fablab-wue/piTelex.supplement/PCB_KiCad/piTelex_TW39_2.1.0/PDF/piTelex_TW39_2.1.0.pdf

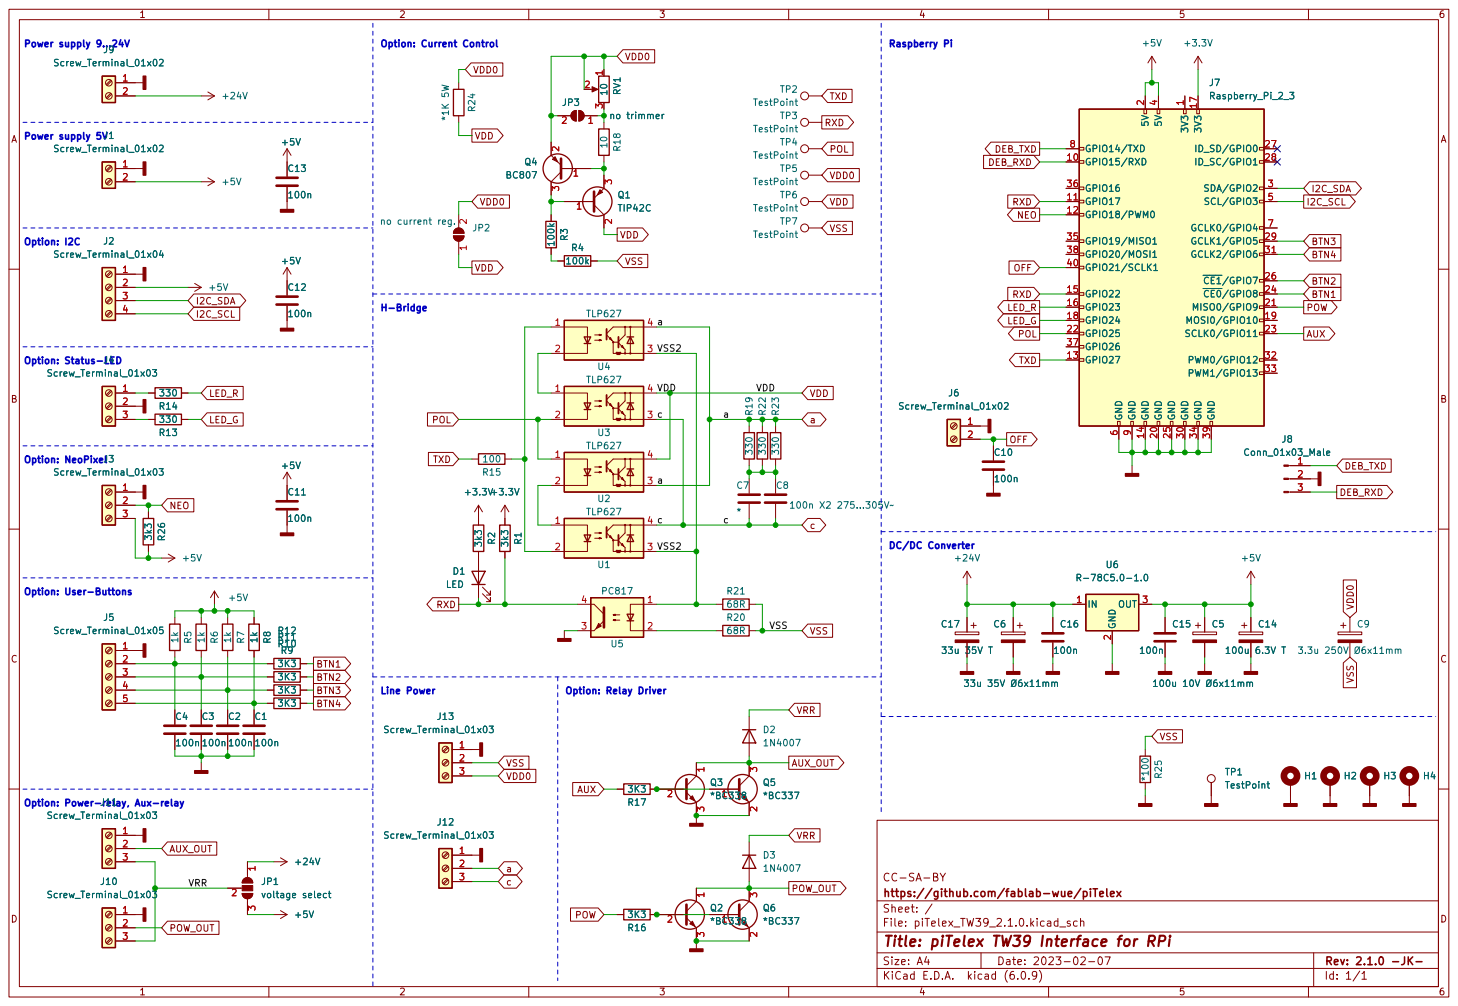
[picture p4: page 1]

File: piTelex_TW39_2.1.0.kicad_sch Sheet: / https://github.com/fablab-wue/piTelex CC-SA-BY

Id: 1/1 Title: piTelex TW39 Interface for RPi
