fablab-wue/piTelex.supplement/PCB_KiCad/SEU-M_1.04/PDF/SEU-M_1.04-B_Cu.pdf

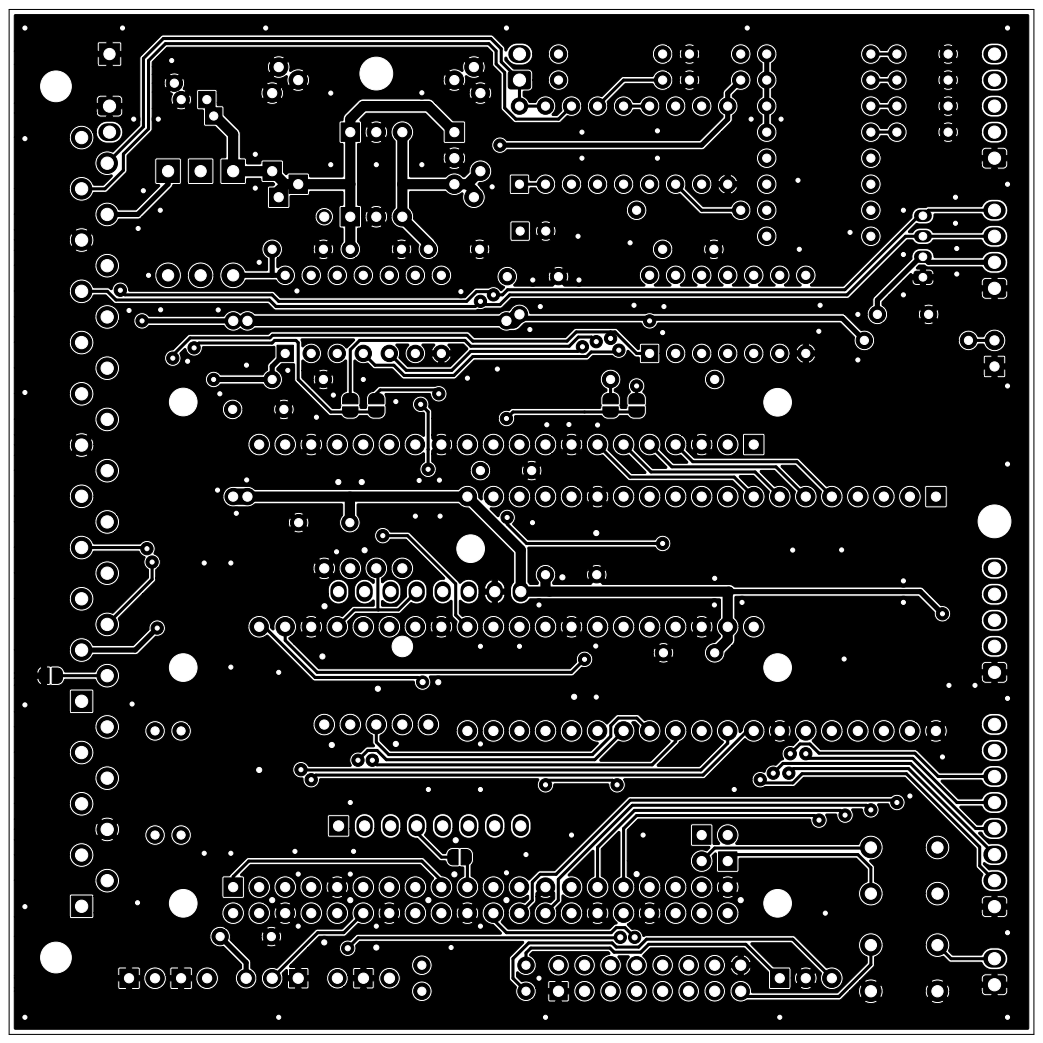
[picture p5: page 1]

File: SEU-M_1.04.kicad_pcb Sheet: Open Hardware
