fablab-wue/piTelex.supplement/PCB_KiCad/SEU-M_1.04/PDF/SEU-M_1.04-F_Cu.pdf

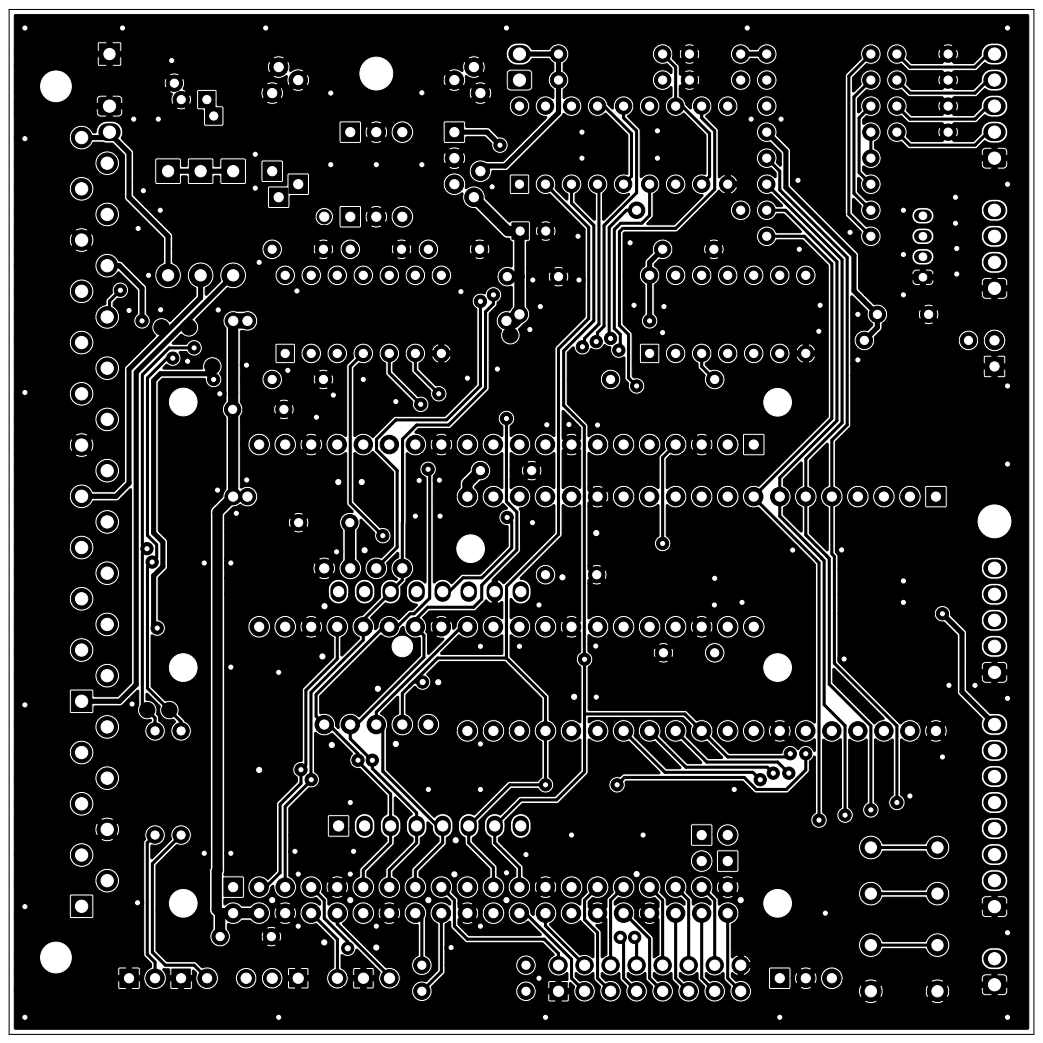
[picture p6: page 1]

File: SEU-M_1.04.kicad_pcb Sheet: Open Hardware
