fablab-wue/piTelex.supplement/PCB_KiCad/SEU-M_1.04/PDF/SEU-M_1.04-F_Fab.pdf

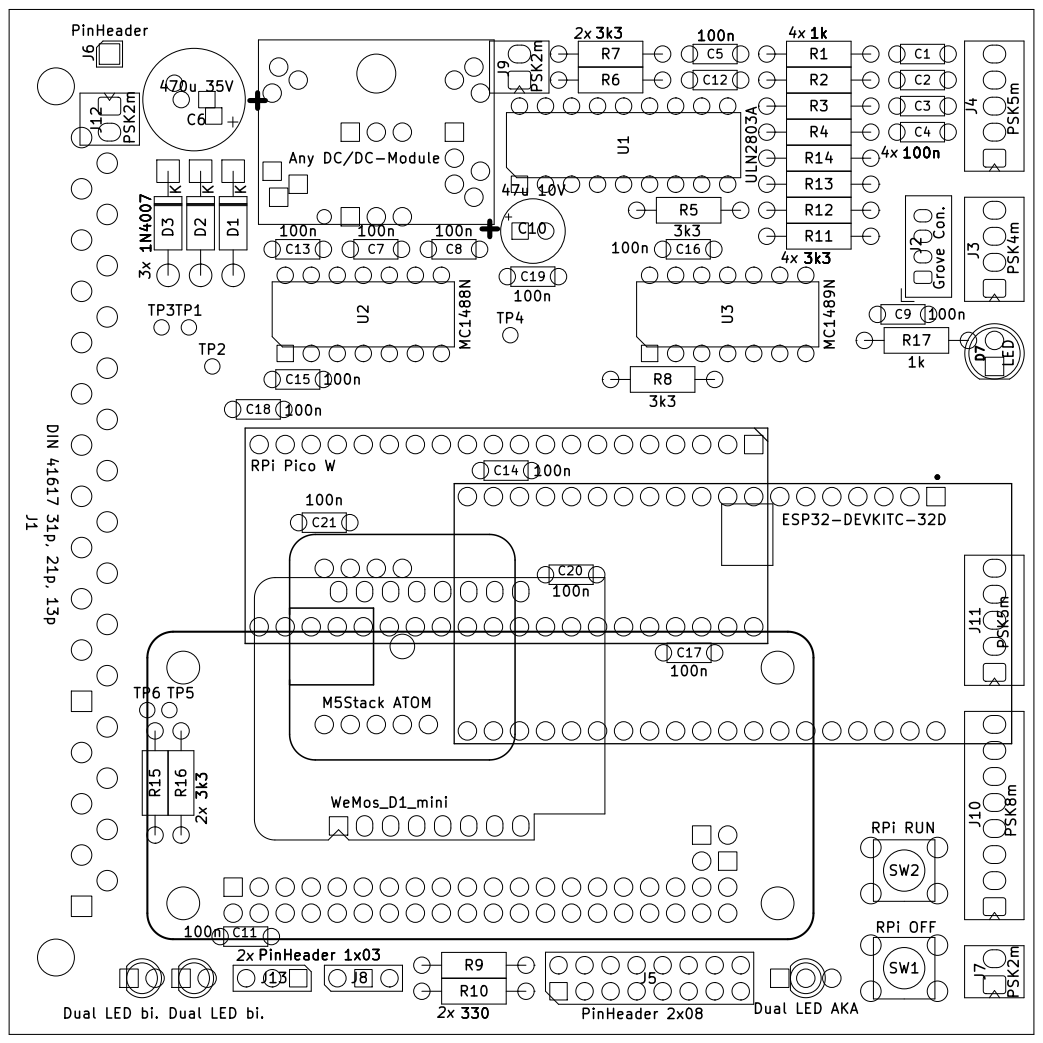
[picture p7: page 1]

SW2 Dual LED bi. PinHeader 1x03

File: SEU-M_1.04.kicad_pcb Sheet: Open Hardware
