fablab-wue/piTelex.supplement/PCB_KiCad/SEU-M_1.04/PDF/SEU-M_1.04-F_Silkscreen.pdf

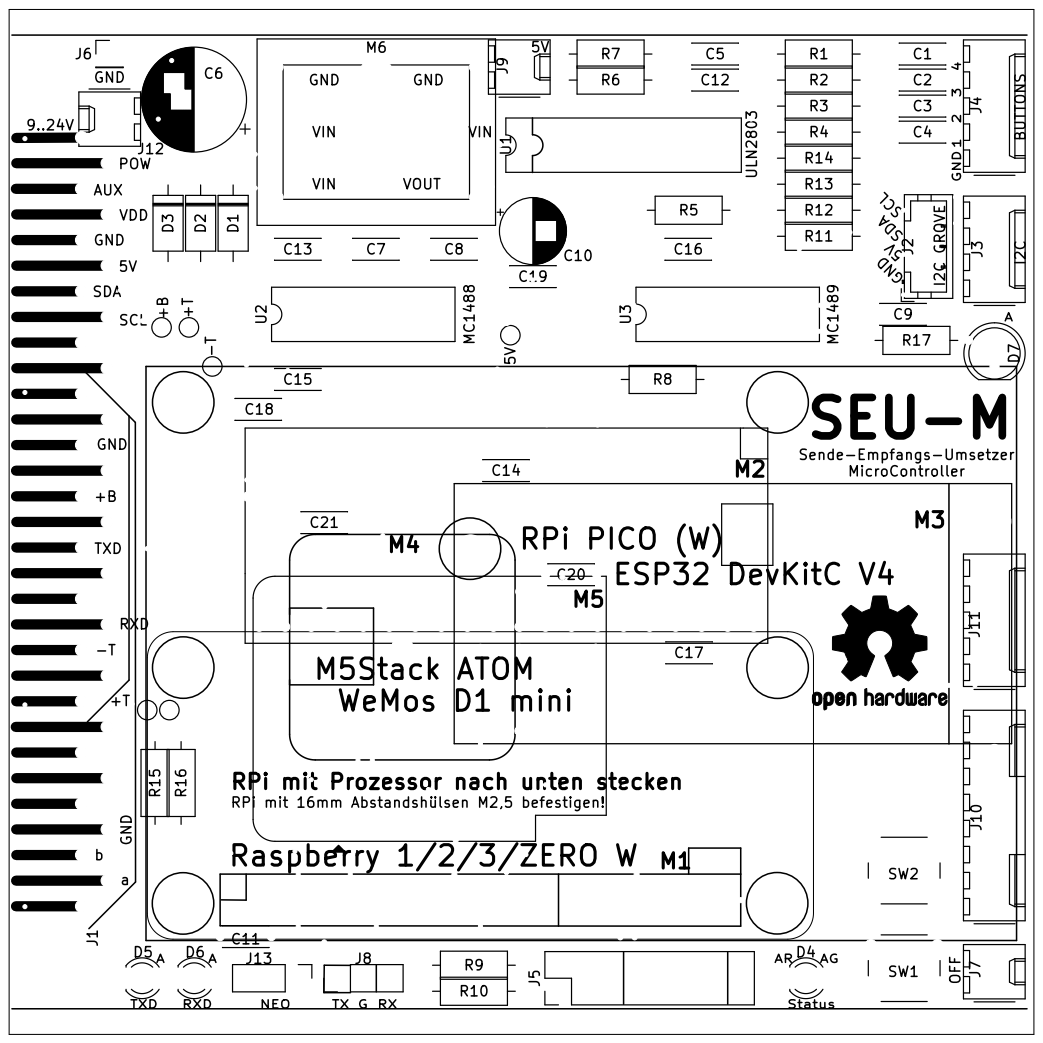
[picture p8: page 1]

3 M5Stack ATOM +T AUXRXD ESP32 DevKitC V4 +B GND

StatusSende-Empfangs-Umsetzer MicroController NEO

File: SEU-M_1.04.kicad_pcb Sheet: Open Hardware
