fablab-wue/piTelex.supplement/PCB_KiCad/SEU-M_1.04/PDF/SEU-M_1.04.pdf

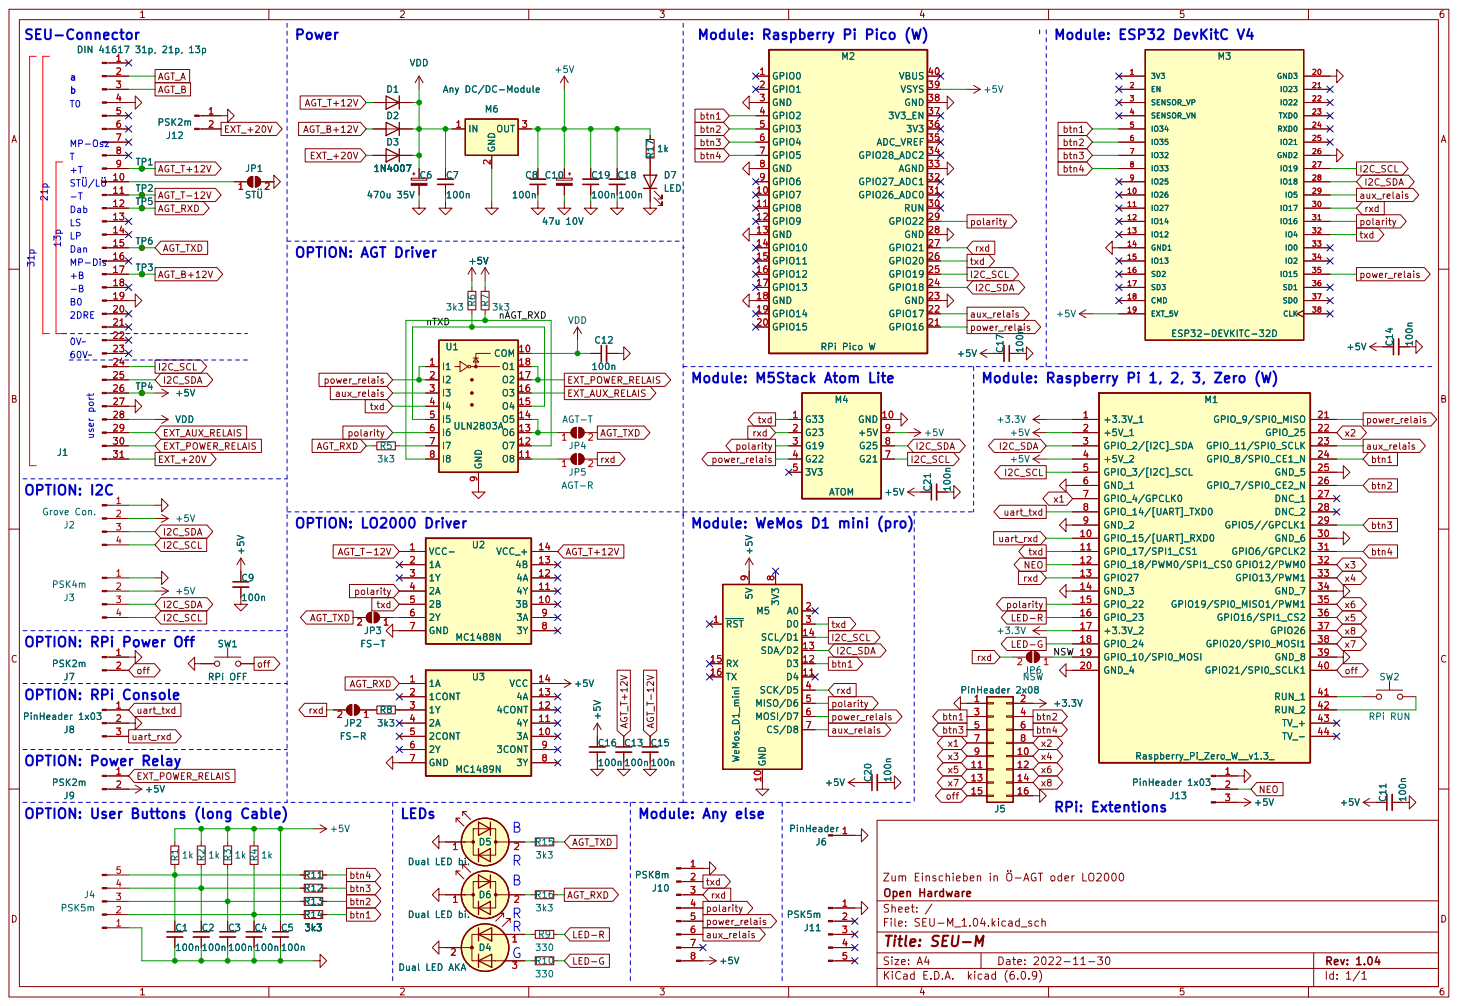
[picture p9: page 1]

SEU-Connector MP-Dis 21p

Module: Raspberry Pi Pico (W)

2 OUT 3 M6 Any DC/DC-Module

M6 Any DC/DC-Module

2 OUT 3 C7
-T OPTION: RPi Power Off

J9 PSK2m
OPTION: User Buttons (long Cable)

File: SEU-M_1.04.kicad_sch Sheet: / Open Hardware
