fablab-wue/piTelex.supplement/PCB_KiCad/piTelex_TW39_2.1.0/PDF/piTelex_TW39_2.1.0-B_Silkscreen.pdf

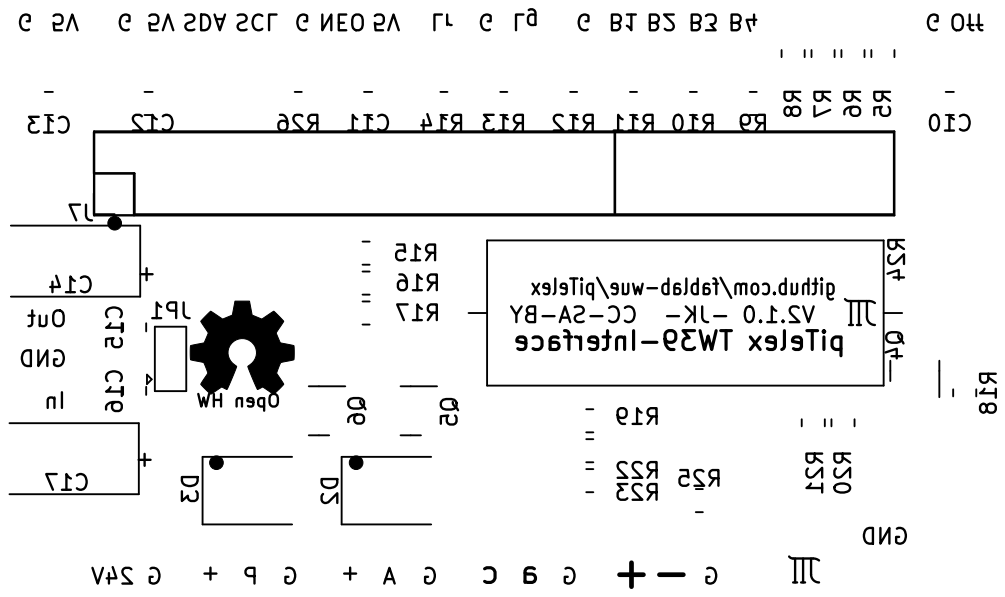
[picture p17: page 1]
