fablab-wue/piTelex.supplement/PCB_KiCad/piTelex_TW39_2.1.0/PDF/piTelex_TW39_2.1.0-F_Cu.pdf

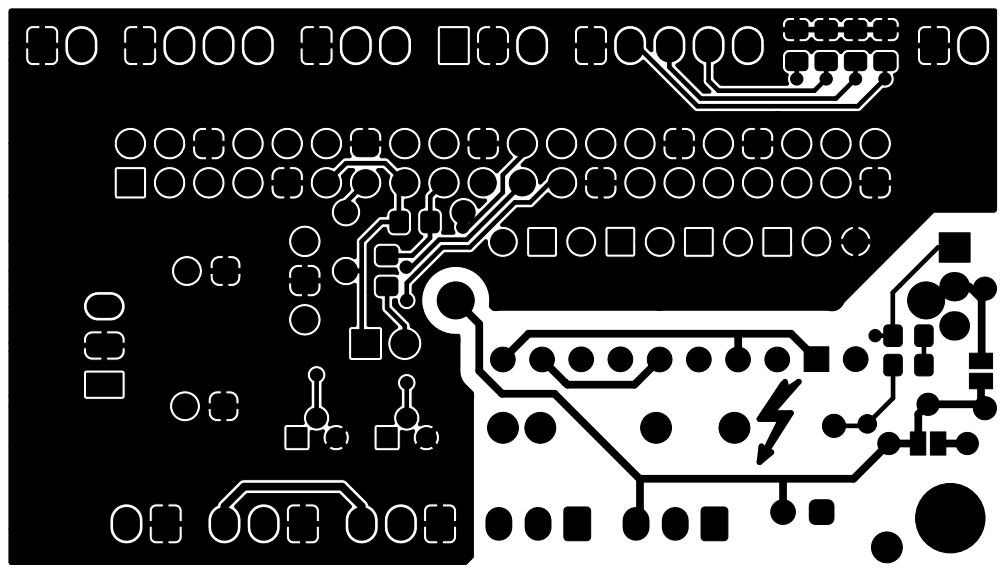
[picture p18: page 1]
