fablab-wue/piTelex.supplement/PCB_KiCad/SEU-M_1.04/PDF/SEU-M_1.04-B_Silkscreen.pdf

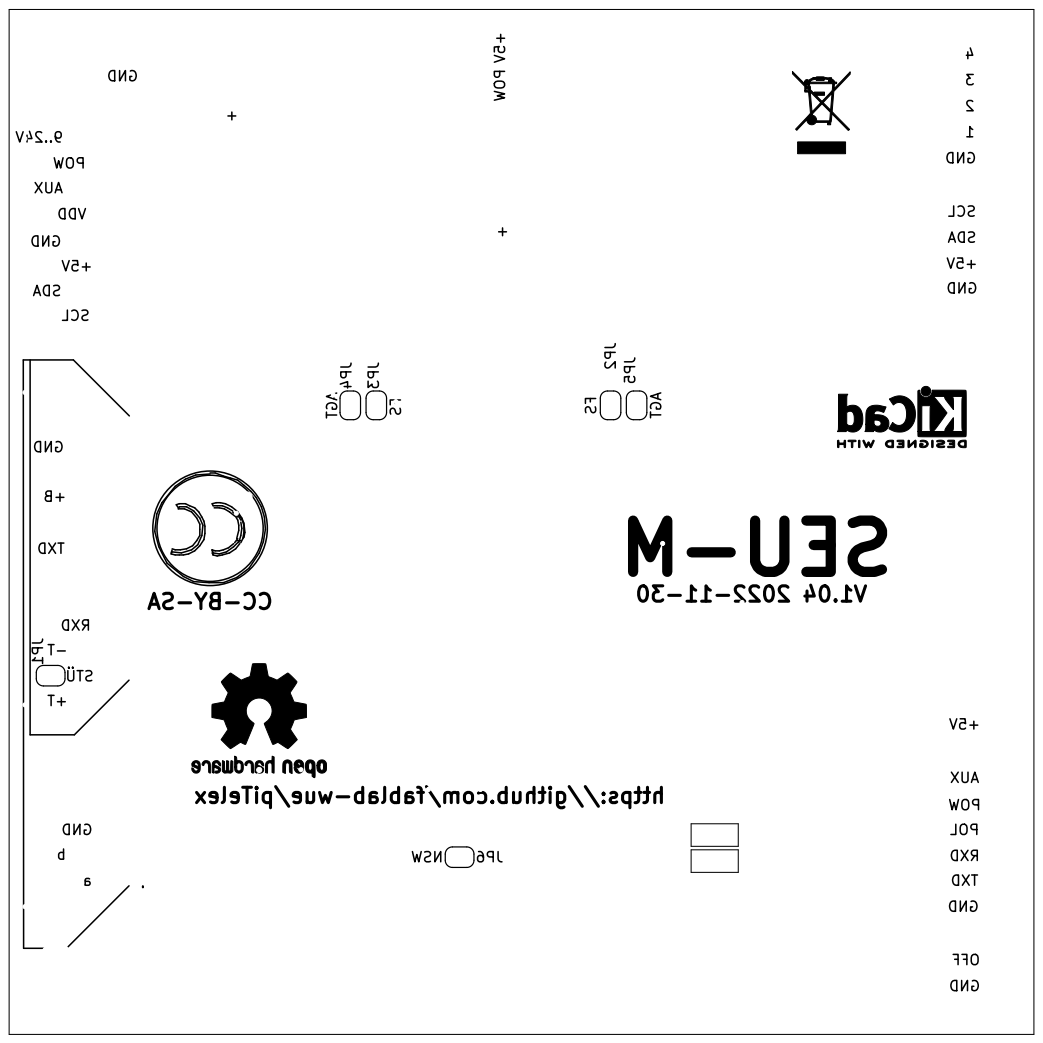
[picture p21: page 1]

AUX https://github.com/fablab-wue/piTelex AGT VDD
